ephemerkey/ephemerkey/firmware/ephemerkey-rs/src/gnss.rs

//! MAX-M10S GNSS: USART1 NMEA link + reset / EXTINT control + 1 PPS.
//!
//! Parses RMC sentences off the UART and, on each valid fix, disciplines the
//! RTC ([`crate::clock`]) from the timestamp and latches geofence membership
//! ([`crate::gate::set_in_fence`]) by testing the position against the sealed
//! config's zone table. Together those are what [`crate::gate::may_emit`] reads.
//!
//! Power model: the receiver is powered on-demand (user presses the button, we
//! acquire one fix, it powers back down), so the 1 PPS TIMEPULSE (PA0) is only
//! present briefly — it is watched here as a liveness/second marker, never as a
//! required continuous signal. Emission freshness is anchored to the last fix's
//! RTC discipline (see [`crate::gate`]), not to PPS.
//!
//! Coarse for now: the clock is set from the RMC timestamp (good to well under
//! the 30 s TOTP window). Sub-second alignment — applying the pending UTC
//! exactly on the PPS edge, or nudging RTC SHIFTR — is the next refinement; the
//! PPS edge is already surfaced here for it.
#![allow(clippy::too_many_arguments)] // task() takes one peripheral per line

use defmt::{info, warn};
use embassy_futures::select::{select, Either};
use embassy_stm32::exti::{self, ExtiInput};
use embassy_stm32::gpio::{Level, Output, OutputOpenDrain, Pull, Speed};
use embassy_stm32::interrupt::typelevel;
use embassy_stm32::peripherals::{DMA1_CH1, EXTI0, PA0, PA1, PA10, PA4, PA9, USART1};
use embassy_stm32::usart::{self, UartRx};
use embassy_stm32::{bind_interrupts, dma, interrupt, Peri};
use embassy_time::Timer;

use crate::{clock, gate};

bind_interrupts!(struct Irqs {
    USART1 => usart::InterruptHandler<USART1>;
    DMA1_CHANNEL1 => dma::InterruptHandler<DMA1_CH1>;
    EXTI0_1 => exti::InterruptHandler<typelevel::EXTI0_1>; // PA0 = 1 PPS
});

// Silence the "unused typelevel interrupt" path — bind_interrupts consumes it.
#[allow(unused_imports)]
use interrupt::typelevel::Interrupt as _;

// An NMEA sentence is at most 82 chars incl. the leading '$' and trailing CRLF.
const LINE_MAX: usize = 96;

#[embassy_executor::task]
pub async fn task(
    uart: Peri<'static, USART1>,
    tx: Peri<'static, PA9>,
    rx: Peri<'static, PA10>,
    reset_n: Peri<'static, PA4>,
    extint: Peri<'static, PA1>,
    rx_dma: Peri<'static, DMA1_CH1>,
    pps: Peri<'static, PA0>,
    pps_exti: Peri<'static, EXTI0>,
) {
    // RESET_N: open-drain into the module (it has its own pull-up).
    // EXTINT: wake / time-mark output to the module.
    let mut reset_n = OutputOpenDrain::new(reset_n, Level::Low, Speed::Low);
    let _extint = Output::new(extint, Level::Low, Speed::Low);

    // TX (PA9) is parked until we send UBX config; claiming it here keeps the
    // pin owned by this task.
    let _tx = tx;

    // 1 PPS TIMEPULSE on PA0 (external signal; no internal pull).
    let mut pps = ExtiInput::new(pps, pps_exti, Pull::None, Irqs);

    // Hold the module in reset briefly, then release.
    Timer::after_millis(10).await;
    reset_n.set_high();
    info!("gnss: reset released");

    // M10 default: 9600 baud NMEA, RX on DMA.
    let mut ucfg = usart::Config::default();
    ucfg.baudrate = 9600;
    let mut rx: UartRx<'static, _> = match UartRx::new(uart, rx, rx_dma, Irqs, ucfg) {
        Ok(r) => r,
        Err(_) => {
            warn!("gnss: uart init failed");
            return;
        }
    };

    let mut buf = [0u8; 128];
    let mut line = [0u8; LINE_MAX];
    let mut ll = 0usize;
    loop {
        match select(rx.read_until_idle(&mut buf), pps.wait_for_rising_edge()).await {
            Either::First(Ok(n)) => feed(&buf[..n], &mut line, &mut ll),
            Either::First(Err(e)) => warn!("gnss: rx error {}", e),
            Either::Second(()) => {
                // PPS rising edge: the receiver is alive and marking the UTC
                // second boundary. TODO: apply the pending fix exactly here for
                // sub-second accuracy. Coarse RMC discipline is already active.
            }
        }
    }
}

/// Accumulate UART bytes into NMEA lines; on each complete line, parse RMC and —
/// on a valid fix — discipline the clock and latch geofence membership. The
/// gate owns the zone table and does the fence test ([`gate::update_from_fix`]).
fn feed(chunk: &[u8], line: &mut [u8; LINE_MAX], ll: &mut usize) {
    for &b in chunk {
        if b == b'\n' || b == b'\r' {
            if *ll > 0 {
                if let Some(fix) = ephemerkey_nmea::parse_rmc(&line[..*ll]) {
                    // A code may emit only from a valid fix INSIDE a fence. An
                    // invalid/void fix (or one outside every zone) closes the
                    // gate at once; the clock then ages out on its own.
                    gate::update_from_fix(fix.valid, fix.lat_e7, fix.lon_e7);
                    if fix.valid {
                        clock::discipline_utc(fix.year, fix.month, fix.day, fix.hour, fix.min, fix.sec);
                        info!(
                            "gnss: fix {}.{:07},{}.{:07}",
                            fix.lat_e7 / 10_000_000,
                            (fix.lat_e7 % 10_000_000).abs(),
                            fix.lon_e7 / 10_000_000,
                            (fix.lon_e7 % 10_000_000).abs(),
                        );
                    }
                }
                *ll = 0;
            }
        } else if *ll < LINE_MAX {
            line[*ll] = b;
            *ll += 1;
        } else {
            *ll = 0; // oversized/garbled line — drop it
        }
    }
}
