ephemerkey/ephemerkey/firmware/lock-attiny/src/power.h

/*
 * ephemerkey lock board — boost-rail power control (ATtiny1616)
 *
 *   PA6  SOL_BOOST_EN  -> MT3608 EN
 *   PA1  BOOST_VSEL    -> 6V/12V FB select (Q2) + servo interlock (Q5)
 *
 * The MT3608 makes VSOL. Disabled, its L1+D2 path passes ~Vbat-0.3 V to VSOL
 * (the servo supply). Enabled with VSEL high it regulates VSOL to +12 V for the
 * solenoid. VSEL high also engages the Q5 interlock that force-disables servo
 * power — so 12 V and servo power can never coexist.
 *
 * IMPORTANT: VSOL feeds the servo. After a 12 V solenoid strike, VSOL must be
 * drained back to ~Vbat (boost off + solenoid conducting) BEFORE re-powering the
 * servo. See the main loop's drain phase.
 */
#ifndef POWER_H
#define POWER_H

/* Boost off, VSEL low (6V/interlock clear), pins driven. Call once at boot,
 * before servo/solenoid init. */
void power_init(void);

/* Bring VSOL up to +12 V: select 12 V first (engages servo interlock), then
 * enable the boost. Caller must wait for the rail to ramp (~500 ms). */
void boost_12v_enable(void);

/* Disable the boost and return VSEL low. VSOL then decays toward ~Vbat (drain
 * it through the solenoid before the next servo phase). */
void boost_disable(void);

/* 6 V boosted servo (CFG_SERVO_BOOST): enable the boost at 6 V (BOOST_VSEL LOW,
 * interlock clear) so the servo rail rises to ~6 V while servo power stays
 * enabled. Requires the servo strapped to VSOL (R13, the default strap) and a 6 V servo. Off by
 * default. */
void boost_servo_enable(void);

#endif /* POWER_H */
